christoph-weiser/mpw6/verilog/sarlogic/sarlogic-gl.v

module sarlogic (VGND,
    VPWR,
    cal,
    clk,
    clkc,
    comp,
    en,
    rstn,
    sample,
    valid,
    ctln,
    ctlp,
    result,
    trim,
    trimb);
 input VGND;
 input VPWR;
 input cal;
 input clk;
 output clkc;
 input comp;
 input en;
 input rstn;
 output sample;
 output valid;
 output [9:0] ctln;
 output [9:0] ctlp;
 output [9:0] result;
 output [4:0] trim;
 output [4:0] trimb;

 wire _000_;
 wire _001_;
 wire _002_;
 wire _003_;
 wire _004_;
 wire _005_;
 wire _006_;
 wire _007_;
 wire _008_;
 wire _009_;
 wire _010_;
 wire _011_;
 wire _012_;
 wire _013_;
 wire _014_;
 wire _015_;
 wire _016_;
 wire _017_;
 wire _018_;
 wire _019_;
 wire _020_;
 wire _021_;
 wire _022_;
 wire _023_;
 wire _024_;
 wire _025_;
 wire _026_;
 wire _027_;
 wire _028_;
 wire _029_;
 wire _030_;
 wire _031_;
 wire _032_;
 wire _033_;
 wire _034_;
 wire _035_;
 wire _036_;
 wire _037_;
 wire _038_;
 wire _039_;
 wire _040_;
 wire _041_;
 wire _042_;
 wire _043_;
 wire _044_;
 wire _045_;
 wire _046_;
 wire _047_;
 wire _048_;
 wire _049_;
 wire _050_;
 wire _051_;
 wire _052_;
 wire _053_;
 wire _054_;
 wire _055_;
 wire _056_;
 wire _057_;
 wire _058_;
 wire _059_;
 wire _060_;
 wire _061_;
 wire _062_;
 wire _063_;
 wire _064_;
 wire _065_;
 wire _066_;
 wire _067_;
 wire _068_;
 wire _069_;
 wire _070_;
 wire _071_;
 wire _072_;
 wire _073_;
 wire _074_;
 wire _075_;
 wire _076_;
 wire _077_;
 wire _078_;
 wire _079_;
 wire _080_;
 wire _081_;
 wire _082_;
 wire _083_;
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
    .VPWR(VPWR),
    .X(trimb[1]));
 sky130_fd_sc_hd__buf_2 output44 (.A(net44),
    .VGND(VGND),
    .VNB(VGND),
    .VPB(VPWR),
    .VPWR(VPWR),
    .X(trimb[2]));
 sky130_fd_sc_hd__buf_2 output45 (.A(net45),
    .VGND(VGND),
    .VNB(VGND),
    .VPB(VPWR),
    .VPWR(VPWR),
    .X(trimb[3]));
 sky130_fd_sc_hd__buf_2 output46 (.A(net46),
    .VGND(VGND),
    .VNB(VGND),
    .VPB(VPWR),
    .VPWR(VPWR),
    .X(trimb[4]));
 sky130_fd_sc_hd__buf_2 output47 (.A(net47),
    .VGND(VGND),
    .VNB(VGND),
    .VPB(VPWR),
    .VPWR(VPWR),
    .X(valid));
 sky130_fd_sc_hd__clkbuf_1 output5 (.A(net5),
    .VGND(VGND),
    .VNB(VGND),
    .VPB(VPWR),
    .VPWR(VPWR),
    .X(clkc));
 sky130_fd_sc_hd__buf_2 output6 (.A(net6),
    .VGND(VGND),
    .VNB(VGND),
    .VPB(VPWR),
    .VPWR(VPWR),
    .X(ctln[0]));
 sky130_fd_sc_hd__buf_2 output7 (.A(net7),
    .VGND(VGND),
    .VNB(VGND),
    .VPB(VPWR),
    .VPWR(VPWR),
    .X(ctln[1]));
 sky130_fd_sc_hd__buf_2 output8 (.A(net8),
    .VGND(VGND),
    .VNB(VGND),
    .VPB(VPWR),
    .VPWR(VPWR),
    .X(ctln[2]));
 sky130_fd_sc_hd__buf_2 output9 (.A(net9),
    .VGND(VGND),
    .VNB(VGND),
    .VPB(VPWR),
    .VPWR(VPWR),
    .X(ctln[3]));
endmodule
